Happily-Coding/SweepyWayBU/ergogen/output/outlines/all_key_clusters_outline.dxf

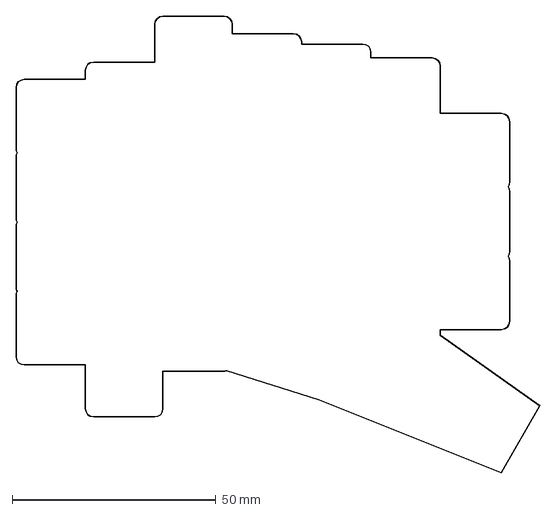
[picture p15: CAD file, 2025-06-28]
ergogen/output/outlines/all_key_clusters_outline.dxf
128.4 x 111.9 mm
