Happily-Coding/SweepyWayBU/ergogen/output/outlines/topleft.dxf

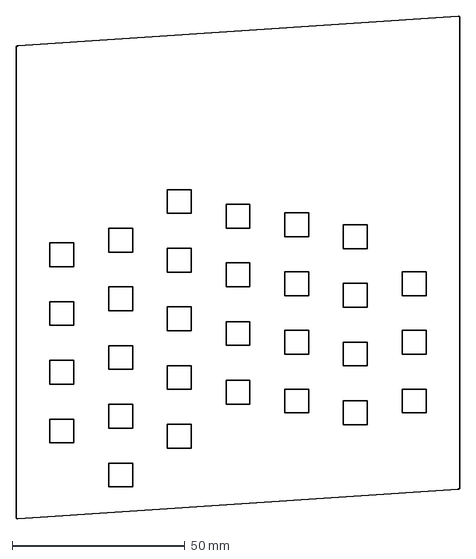
[picture p16: CAD file, 2025-06-28]
ergogen/output/outlines/topleft.dxf
128.5 x 145.6 mm
