Happily-Coding/SweepyWayBU/ergogen/output/outlines/thumb_suplementary_outline.dxf

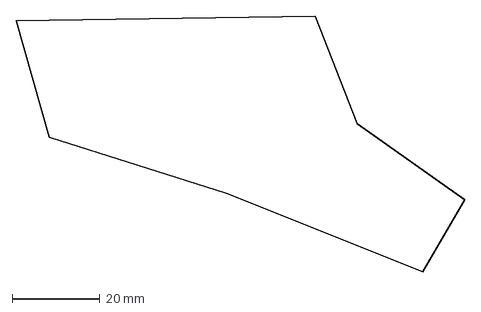
[picture p17: CAD file, 2025-06-28]
ergogen/output/outlines/thumb_suplementary_outline.dxf
101.9 x 58.2 mm
