Happily-Coding/SweepyWayBU/ergogen/output/outlines/combined.dxf

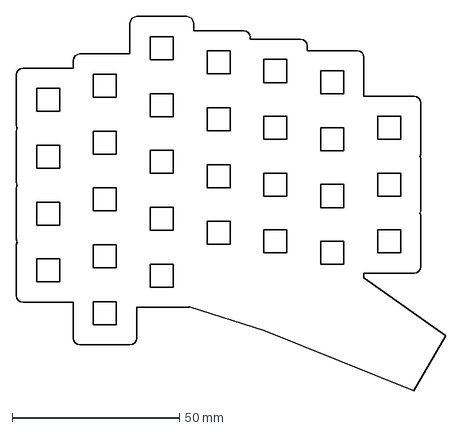
[picture p18: CAD file, 2025-06-28]
ergogen/output/outlines/combined.dxf
128.4 x 111.9 mm
