Happily-Coding/SweepyWayBU/ergogen/output/outlines/r_all_key_clusters_outline.dxf

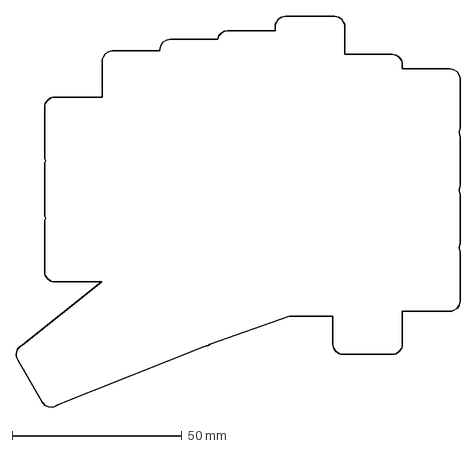
[picture p19: CAD file, 2025-06-28]
ergogen/output/outlines/r_all_key_clusters_outline.dxf
131.0 x 115.7 mm
