Happily-Coding/SweepyWayBU/ergogen/output/outlines/r_key_based_board_outline.dxf

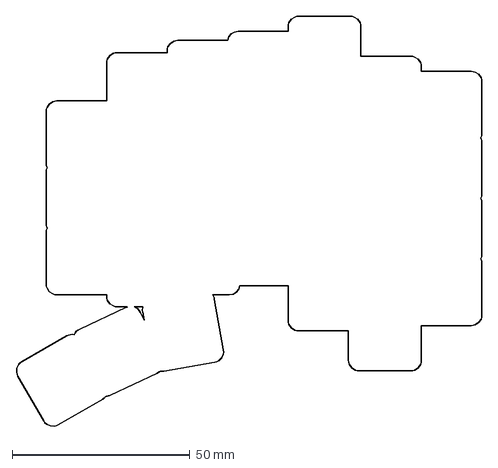
[picture p20: CAD file, 2025-06-28]
ergogen/output/outlines/r_key_based_board_outline.dxf
131.0 x 115.7 mm
