Happily-Coding/SweepyWayBU/ergogen/output/outlines/pcb_left.dxf

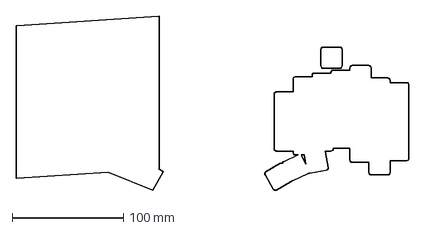
[picture p21: CAD file, 2025-06-28]
ergogen/output/outlines/pcb_left.dxf
352.8 x 156.6 mm
