Happily-Coding/SweepyWayBU/ergogen/output/outlines/l_thumb_suplementary_outline.dxf

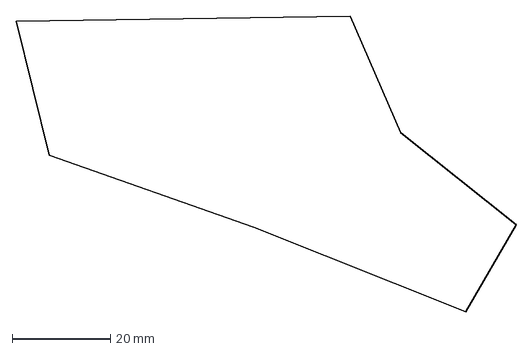
[picture p22: CAD file, 2025-06-28]
ergogen/output/outlines/l_thumb_suplementary_outline.dxf
101.7 x 60.2 mm
