Happily-Coding/SweepyWayBU/ergogen/output/outlines/topright.dxf

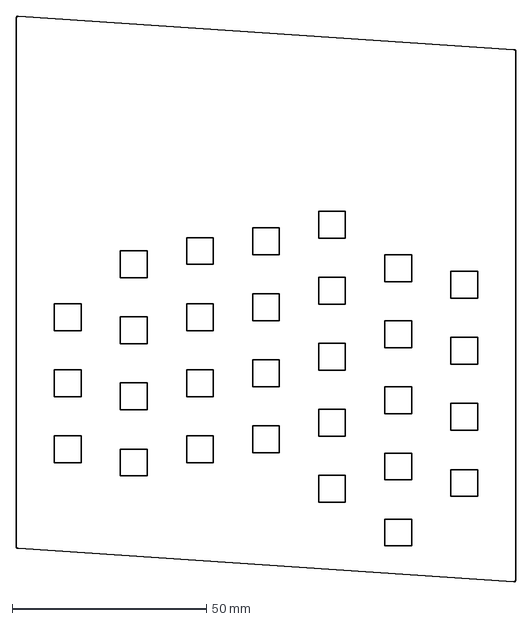
[picture p23: CAD file, 2025-06-28]
ergogen/output/outlines/topright.dxf
128.5 x 145.6 mm
